KonradWF/single-phase-power-meter/SW/SinglePhasePowerMeterProject/Core/Inc/cs5490_c_wrapper.h

#ifndef INC_CS5490_C_WRAPPER_H_
#define INC_CS5490_C_WRAPPER_H_

#ifdef __cplusplus
extern "C" {
#endif


void CS5490_GainCalibrationProcedure();
void CS5490_OffsetCalibrationProcedure();


#ifdef __cplusplus
}
#endif
#endif /* INC_CS5490_C_WRAPPER_H_ */
